msplr/PolyPot/graphics/rendering/adapter.png

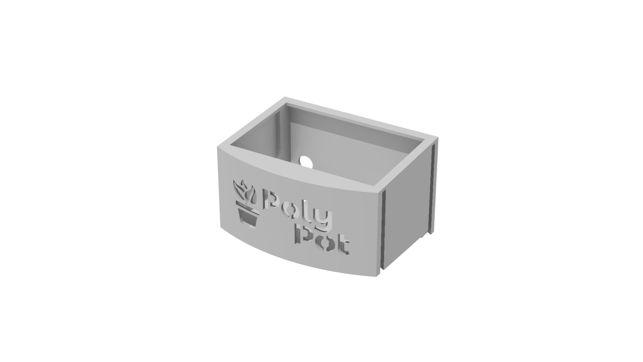
graphics/rendering/adapter.png
