msplr/PolyPot/graphics/rendering/background.png

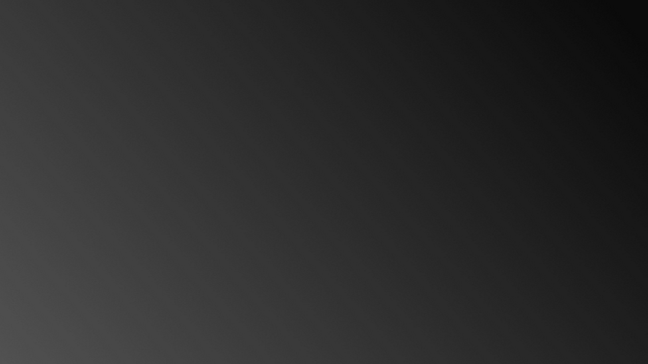
graphics/rendering/background.png
