msplr/PolyPot/graphics/rendering/module.png

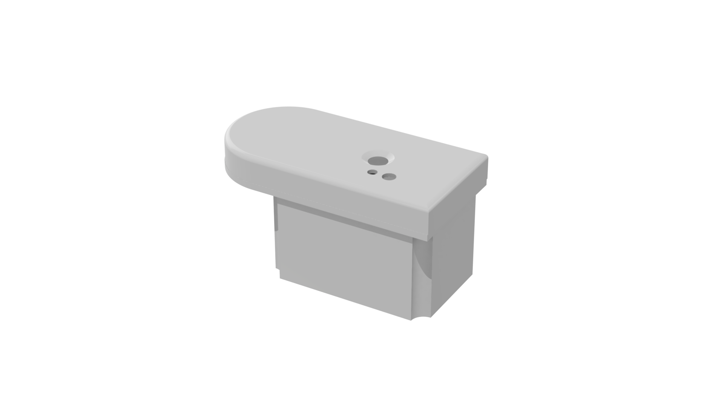
graphics/rendering/module.png
