msplr/PolyPot/graphics/rendering/plant+water_tank+adapter+module.png

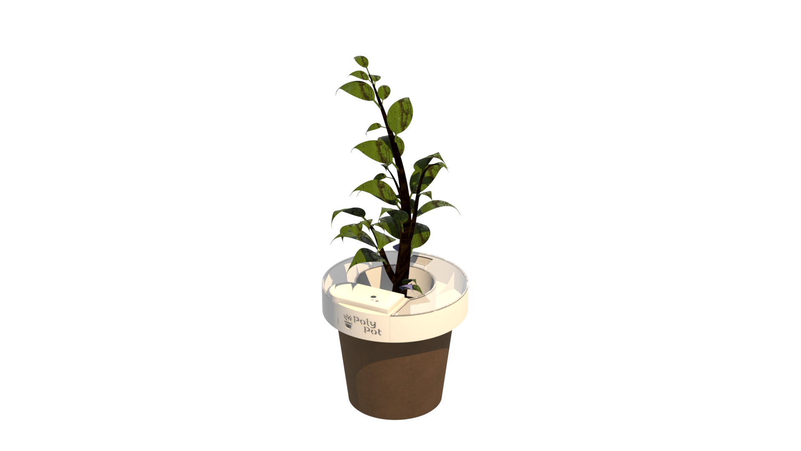
graphics/rendering/plant+water_tank+adapter+module.png
