msplr/PolyPot/graphics/rendering/polypot.png

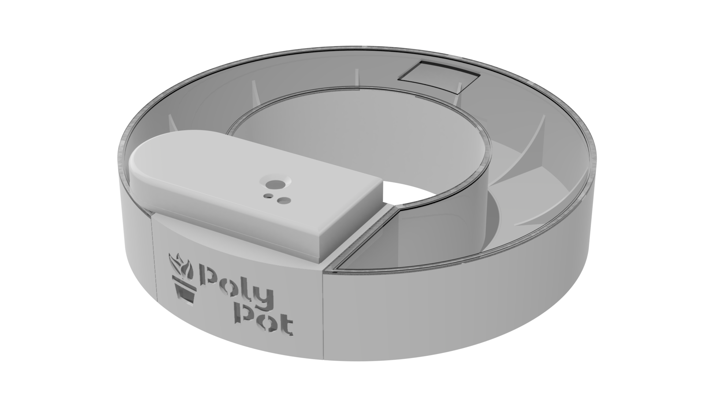
graphics/rendering/polypot.png
