msplr/PolyPot/graphics/rendering/polypot_exploded.png

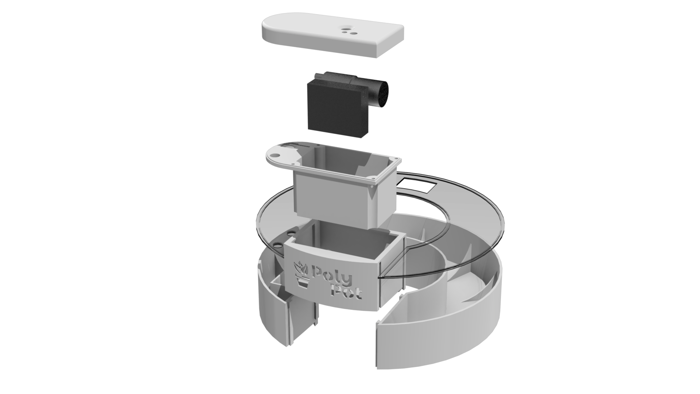
graphics/rendering/polypot_exploded.png
