msplr/PolyPot/graphics/screenshots/configuration.png

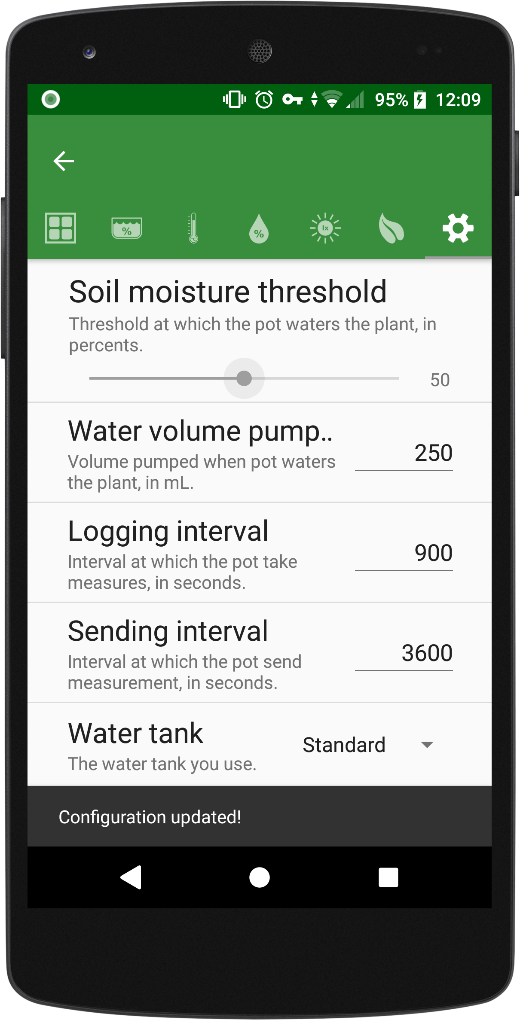
graphics/screenshots/configuration.png
