msplr/PolyPot/graphics/screenshots/features_about.png

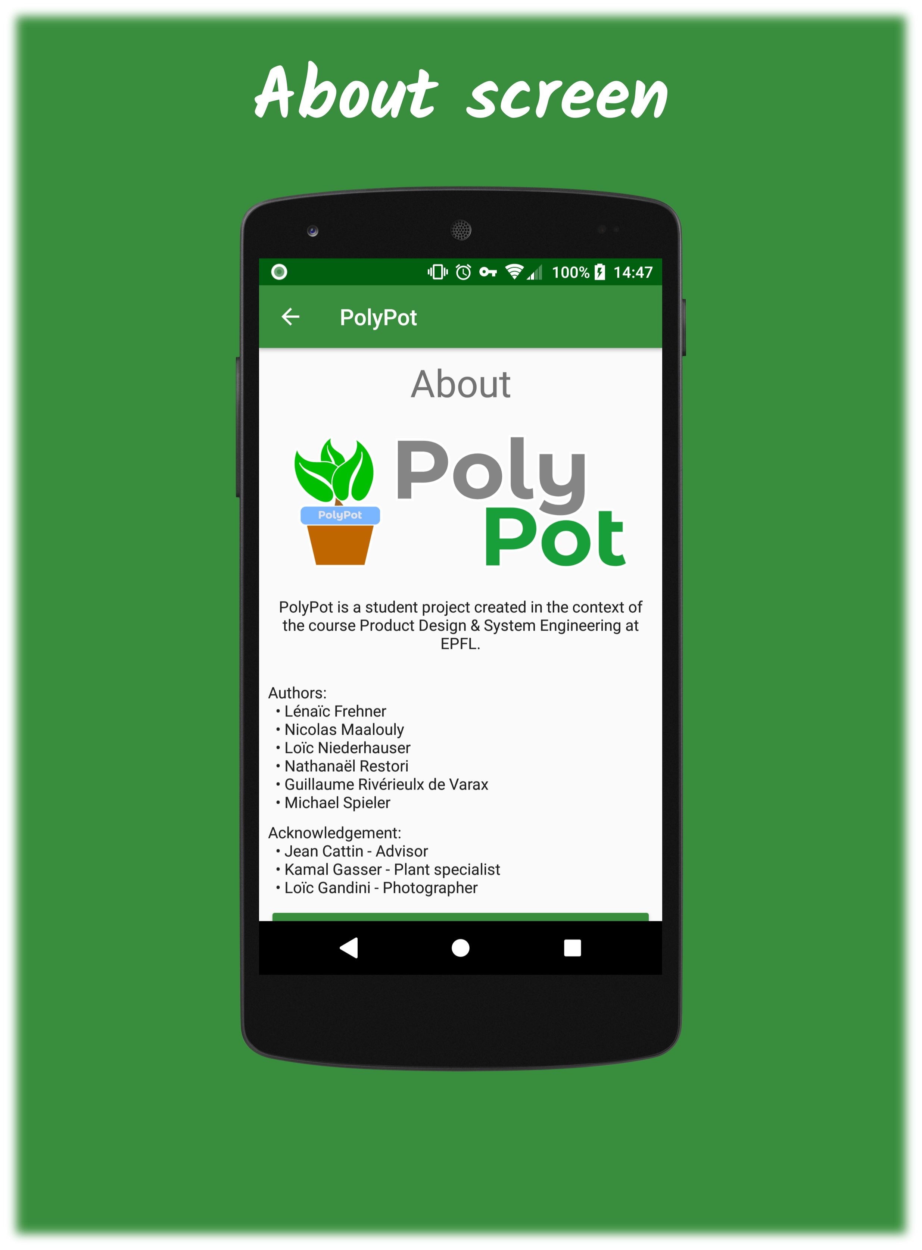
graphics/screenshots/features_about.png
