msplr/PolyPot/graphics/screenshots/features_configuration.png

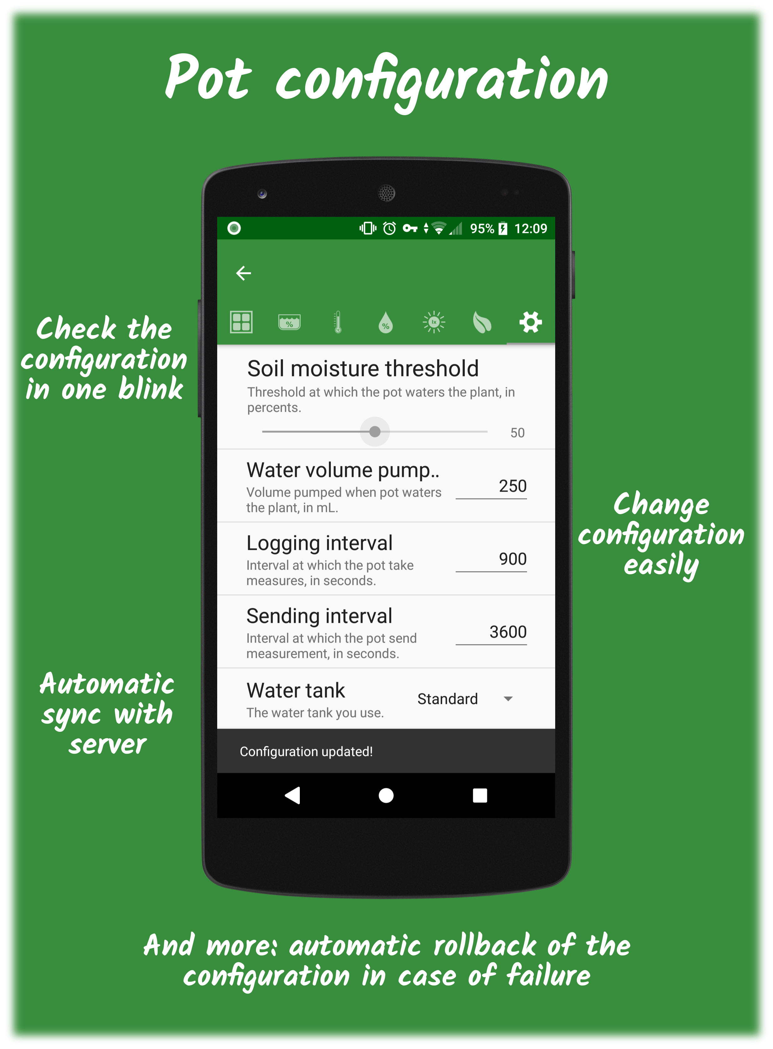
graphics/screenshots/features_configuration.png
