msplr/PolyPot/graphics/screenshots/features_homescreen.png

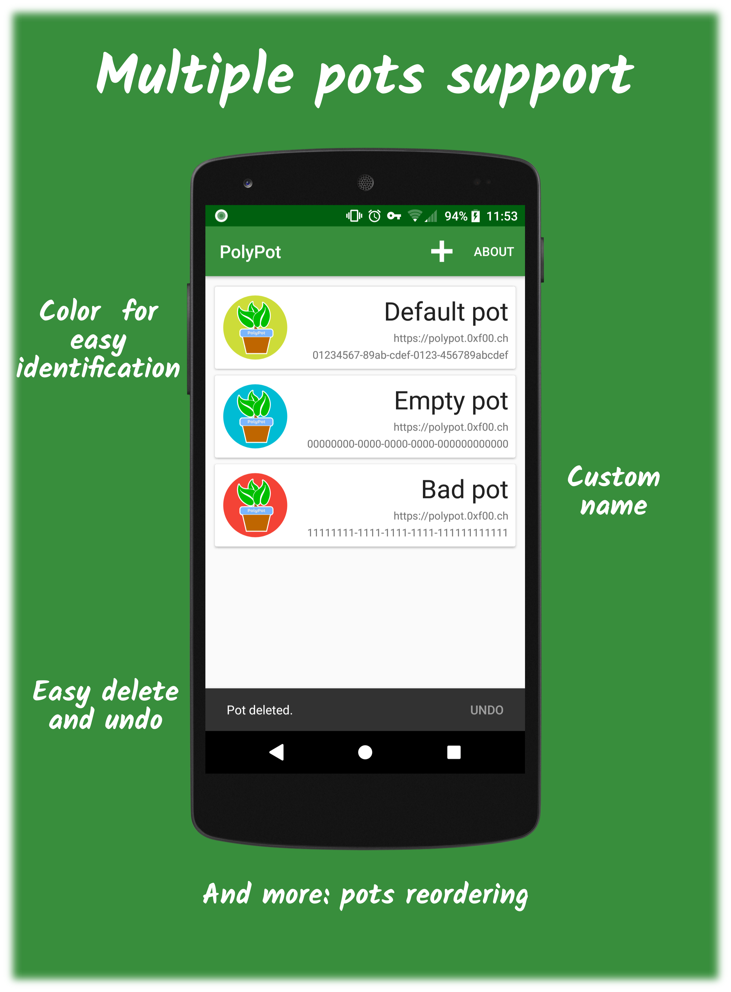
graphics/screenshots/features_homescreen.png
