msplr/PolyPot/graphics/screenshots/features_luminosity.png

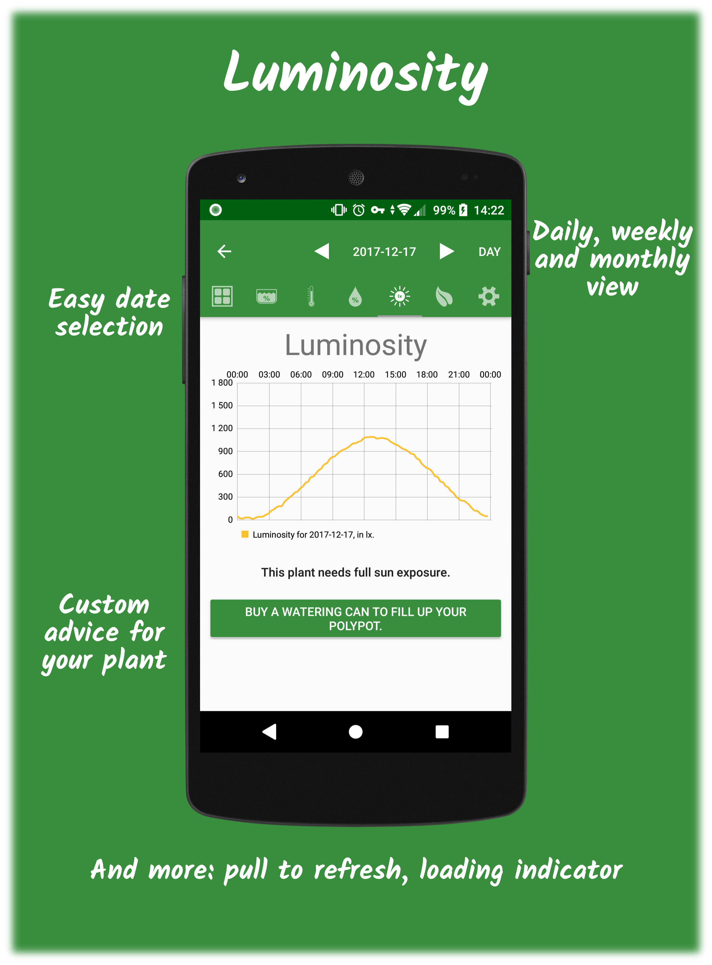
graphics/screenshots/features_luminosity.png
