msplr/PolyPot/graphics/screenshots/features_notifications.png

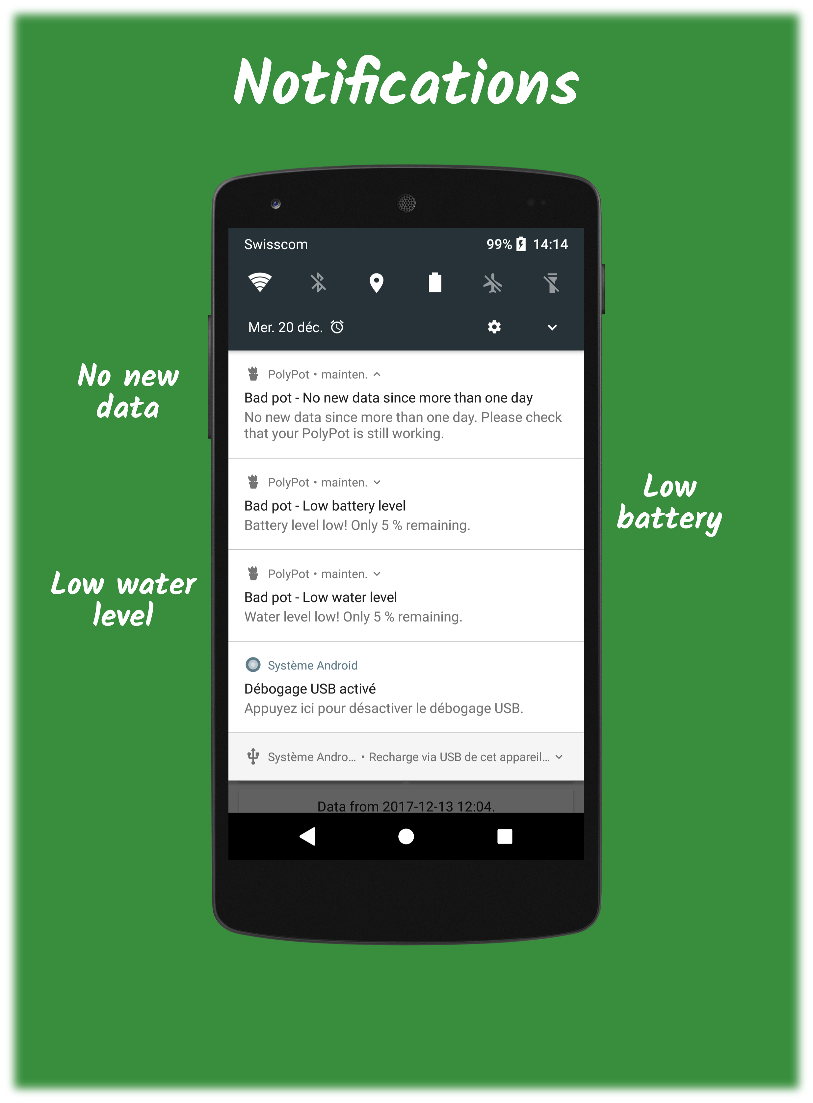
graphics/screenshots/features_notifications.png
