msplr/PolyPot/graphics/screenshots/features_plant.png

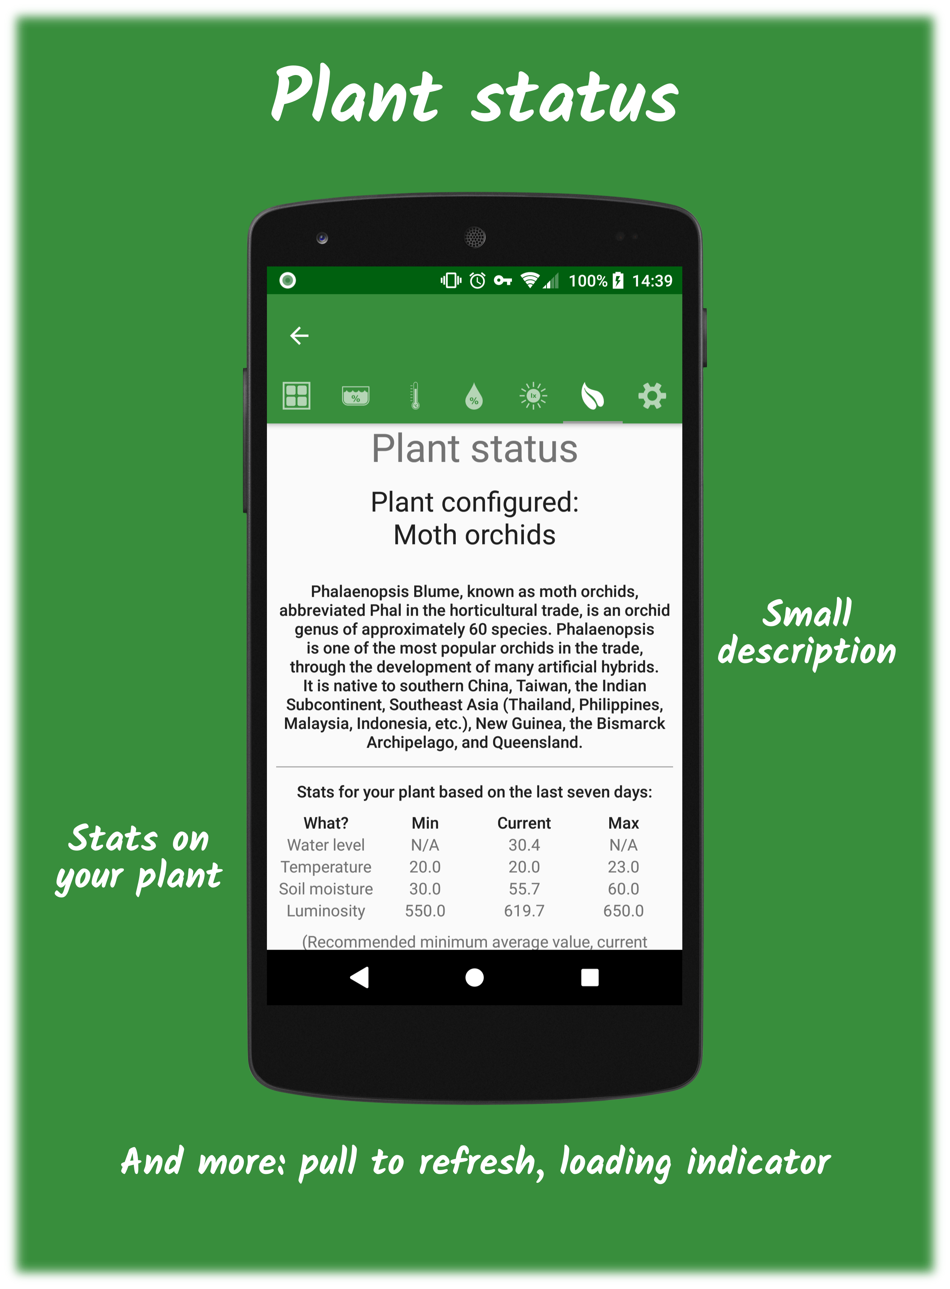
graphics/screenshots/features_plant.png
