msplr/PolyPot/graphics/screenshots/features_summary.png

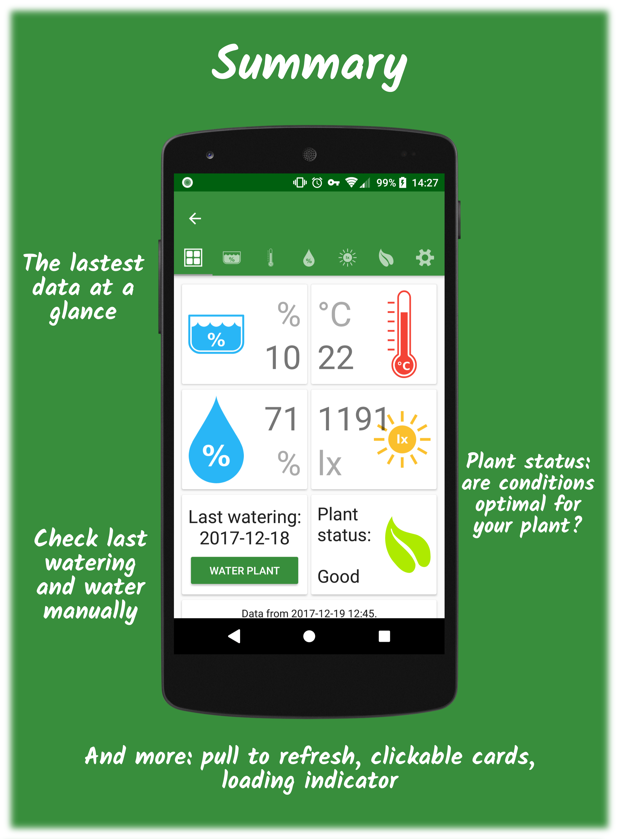
graphics/screenshots/features_summary.png
