msplr/PolyPot/graphics/screenshots/homescreen.png

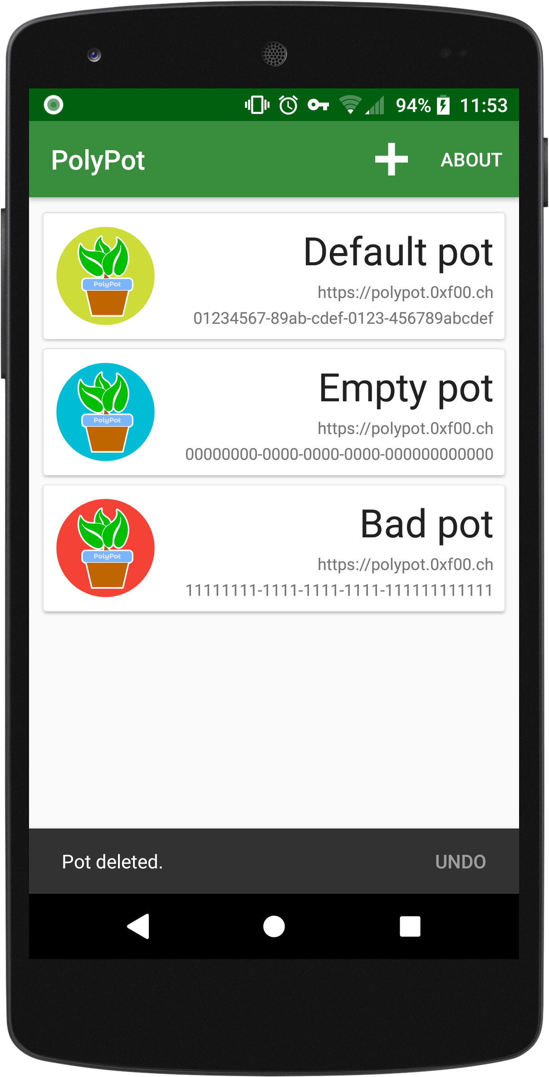
graphics/screenshots/homescreen.png
