msplr/PolyPot/graphics/screenshots/luminosity.png

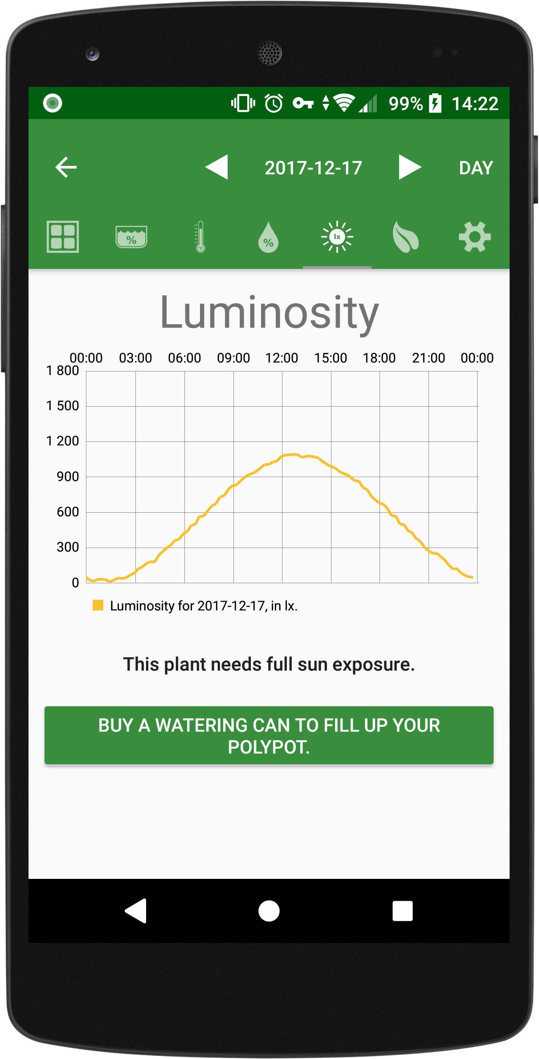
graphics/screenshots/luminosity.png
