msplr/PolyPot/graphics/screenshots/notifications.png

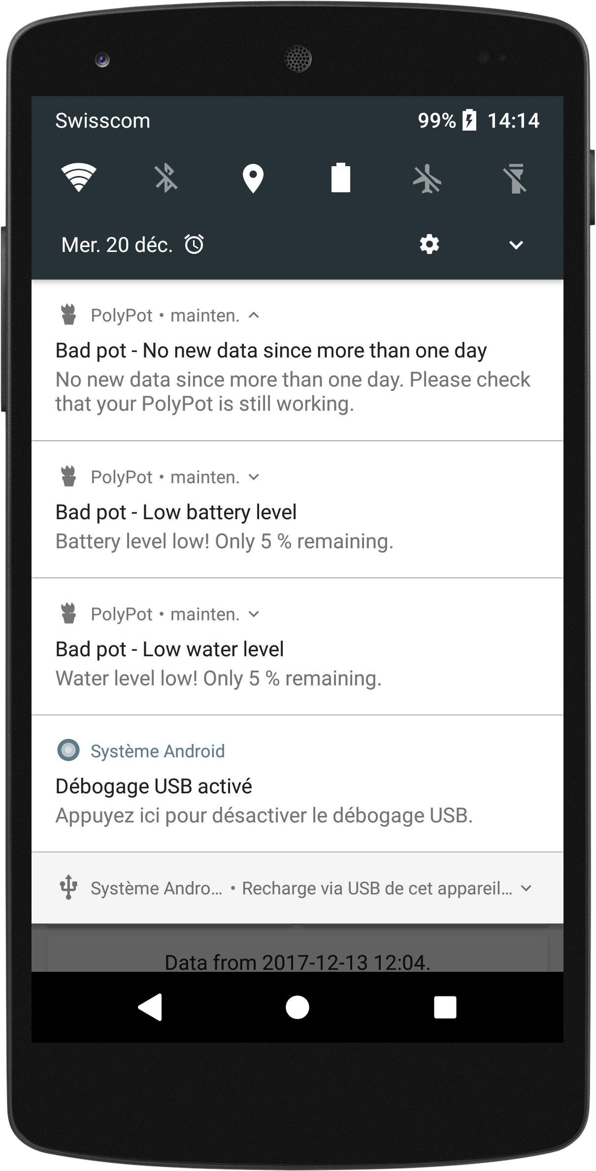
graphics/screenshots/notifications.png
