msplr/PolyPot/graphics/screenshots/plant.png

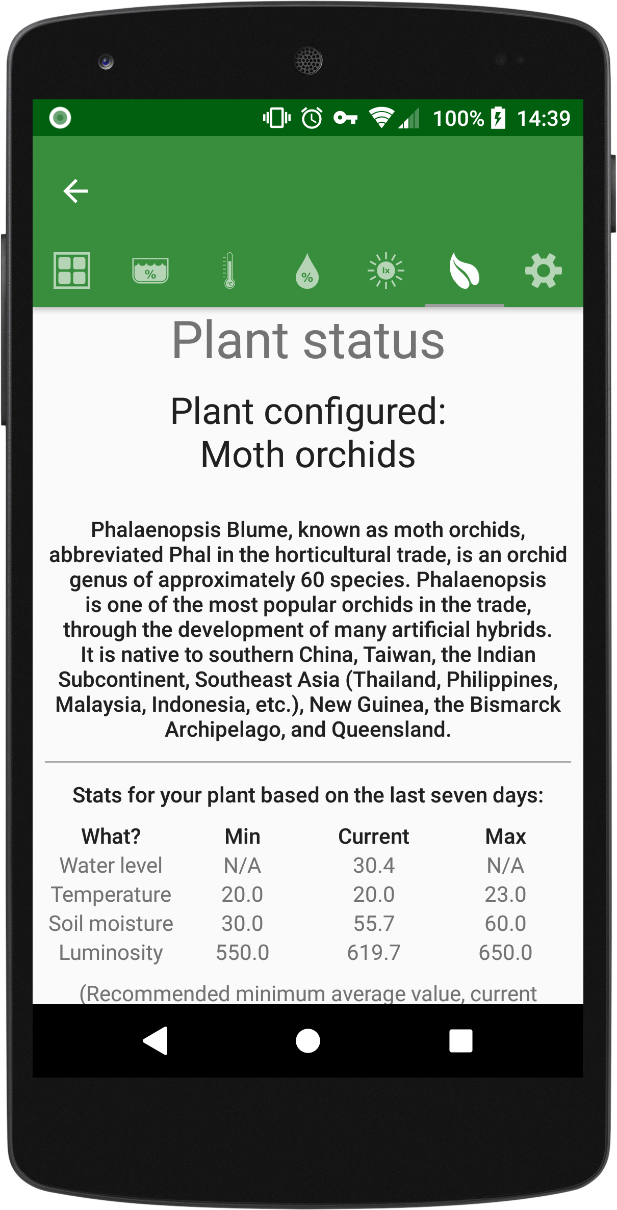
graphics/screenshots/plant.png
