msplr/PolyPot/graphics/screenshots/soil_moisture.png

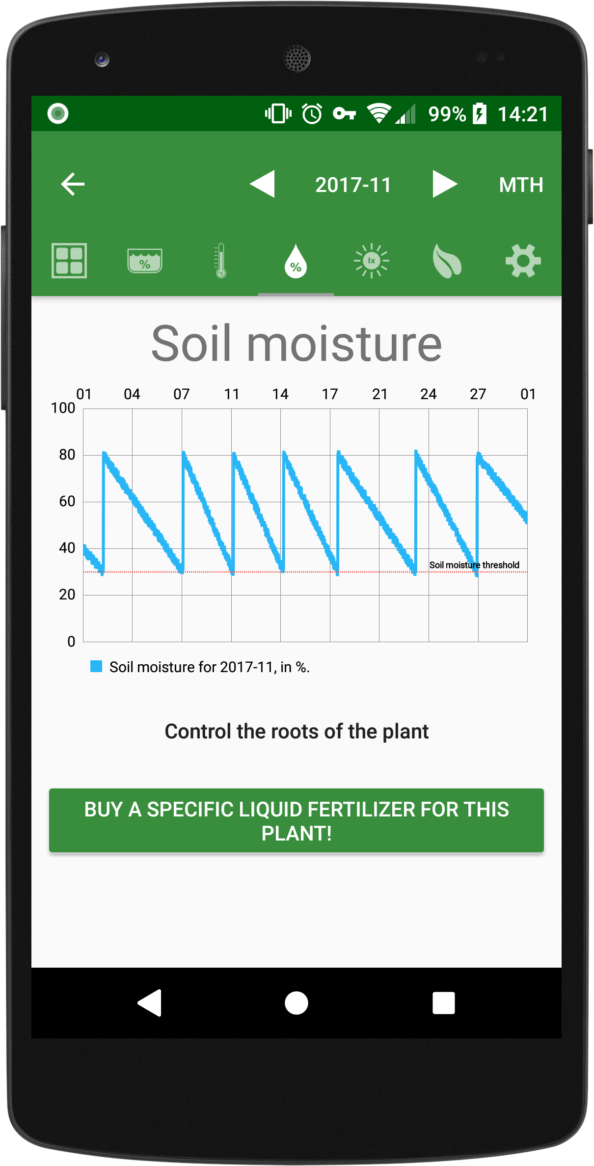
graphics/screenshots/soil_moisture.png
