msplr/PolyPot/graphics/screenshots/summary.png

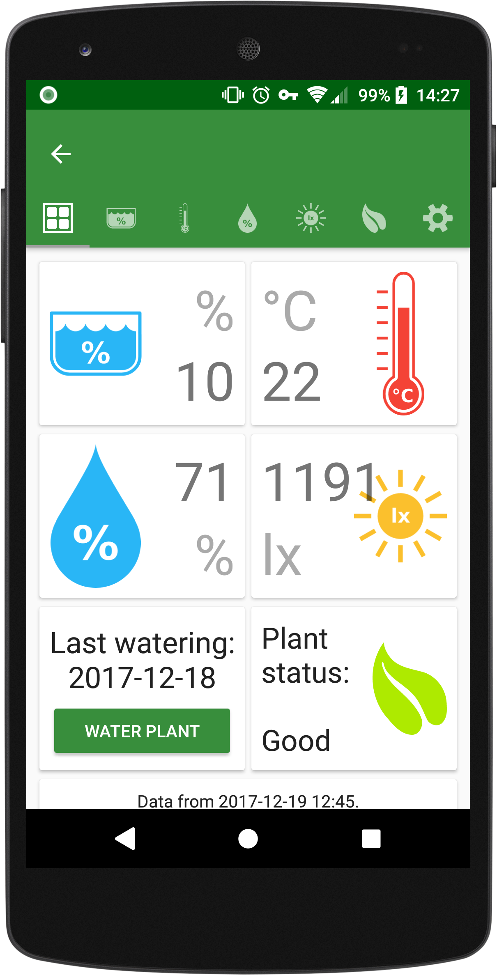
graphics/screenshots/summary.png
