msplr/PolyPot/graphics/screenshots/temperature.png

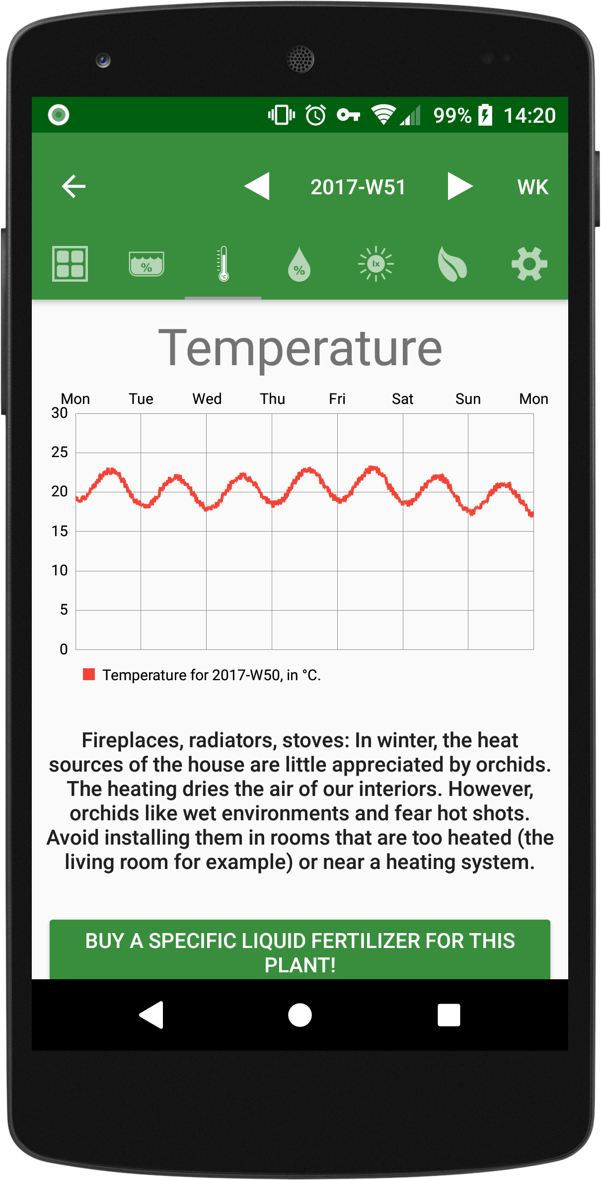
graphics/screenshots/temperature.png
