msplr/PolyPot/graphics/screenshots/water_level.png

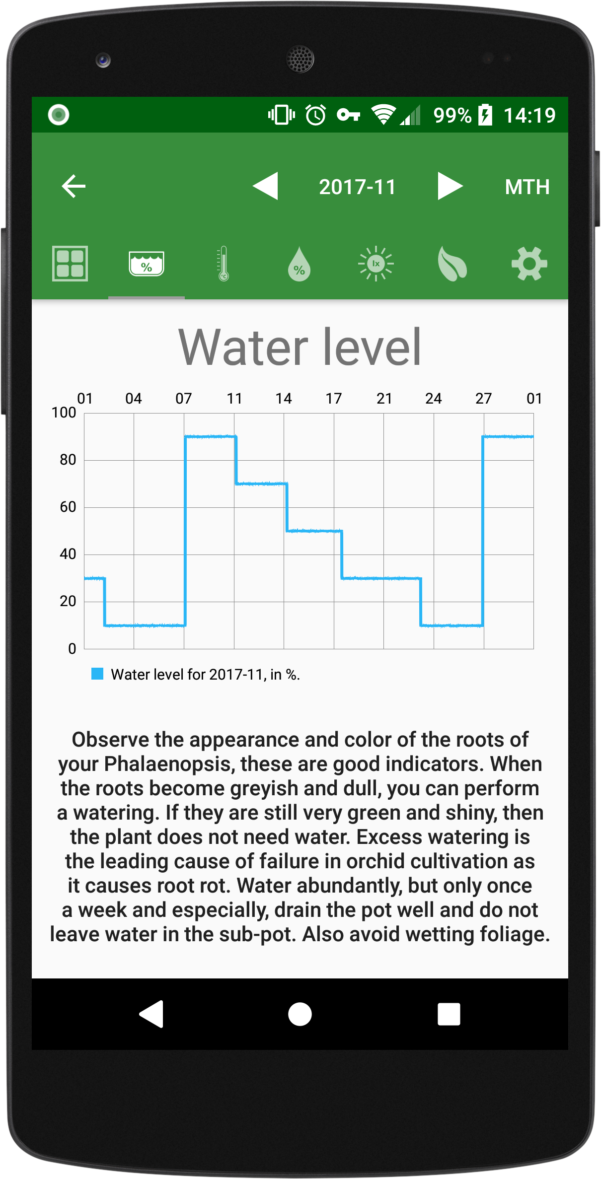
graphics/screenshots/water_level.png
