msplr/PolyPot/graphics/screenshots/features_setup_and_add.png

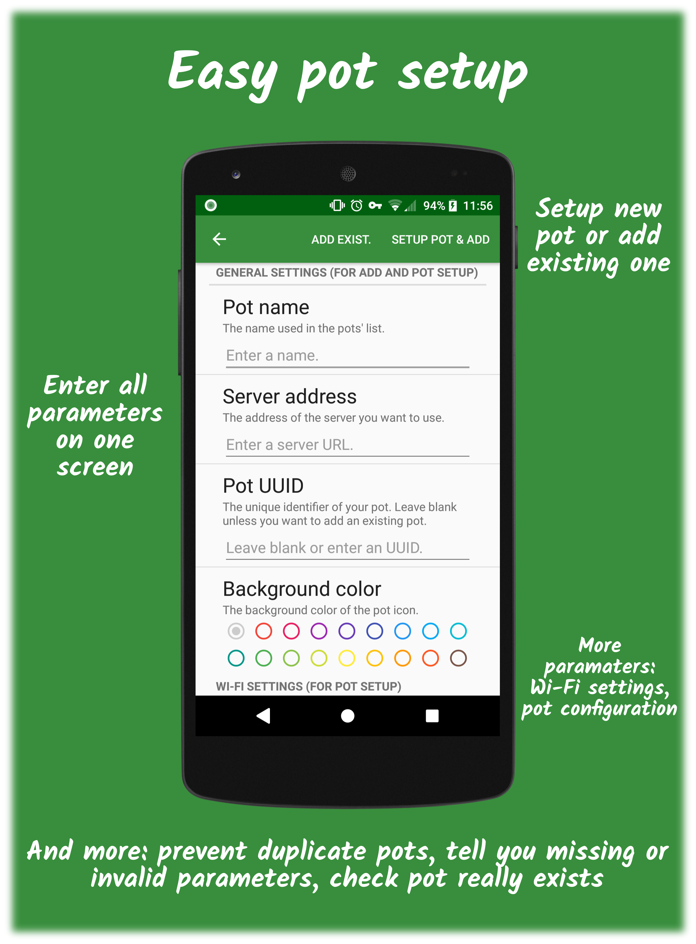
graphics/screenshots/features_setup_and_add.png
