msplr/PolyPot/graphics/screenshots/features_setup_progress.png

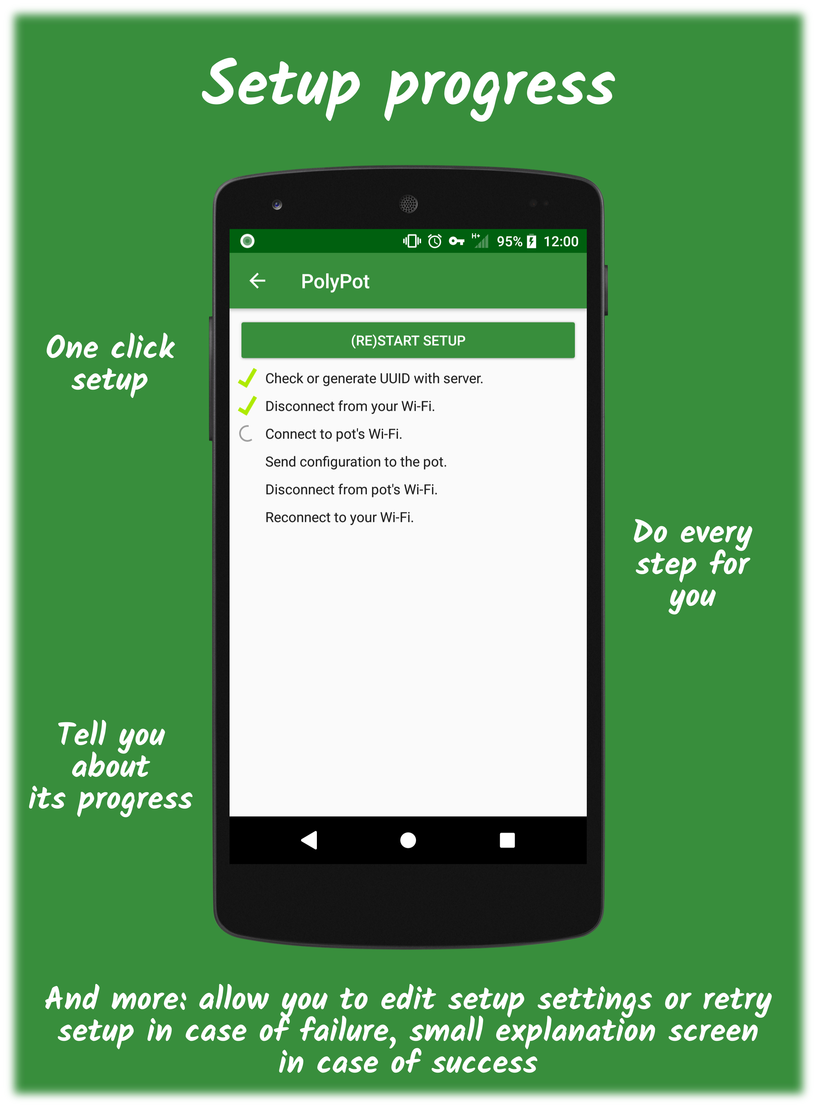
graphics/screenshots/features_setup_progress.png
