msplr/PolyPot/graphics/screenshots/setup_and_add.png

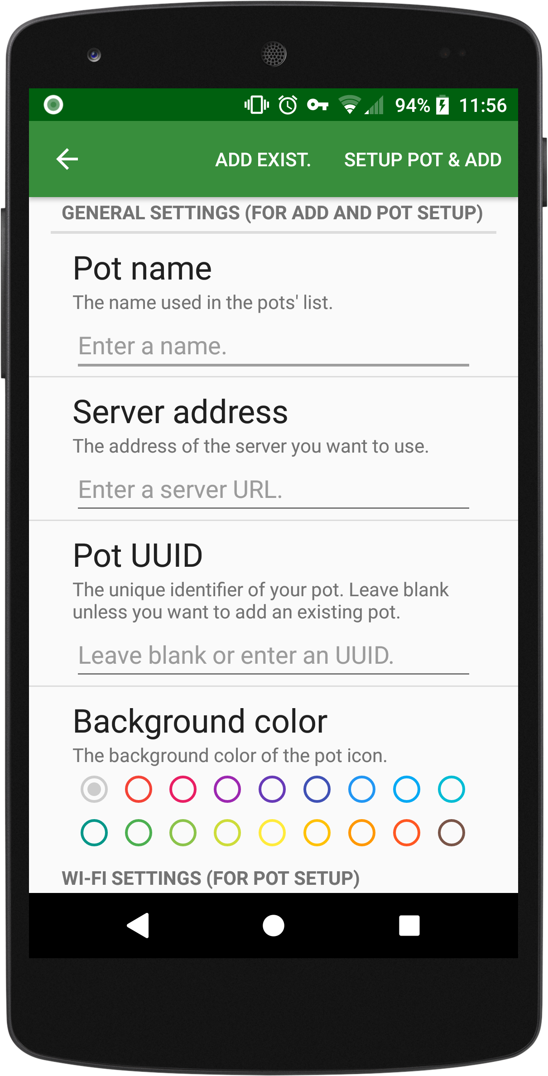
graphics/screenshots/setup_and_add.png
