msplr/PolyPot/graphics/screenshots/setup_progress.png

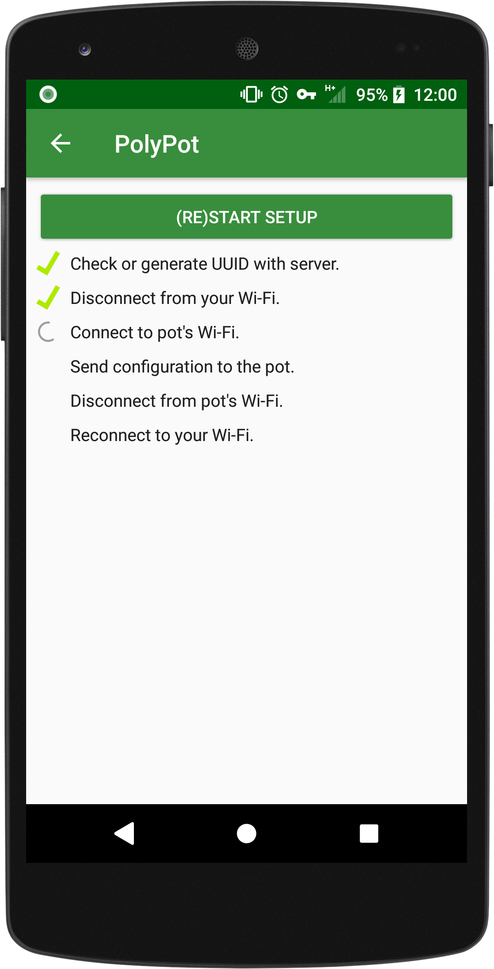
graphics/screenshots/setup_progress.png
