msplr/PolyPot/smartphone/app/src/main/java/ch/epfl/pdse/polypotapp/PreferenceSpinner.java

package ch.epfl.pdse.polypotapp;

import android.content.Context;
import android.content.res.TypedArray;
import android.support.v7.preference.Preference;
import android.support.v7.preference.PreferenceViewHolder;
import android.util.AttributeSet;
import android.view.View;
import android.widget.AdapterView;
import android.widget.ArrayAdapter;
import android.widget.Spinner;

public class PreferenceSpinner extends Preference implements Preference.OnPreferenceChangeListener,AdapterView.OnItemSelectedListener  {
    private Spinner mSpinner;
    private ArrayAdapter<CharSequence> mArrayAdapter;

    private final int mArray;

    private String mValue;

    public PreferenceSpinner(Context context) {
        // Delegate to other constructor
        this(context, null);
    }

    public PreferenceSpinner(Context context, AttributeSet attrs) {
        this(context, attrs, 0);
    }

    public PreferenceSpinner(Context context, AttributeSet attrs, int defStyleAttr) {
        super(context, attrs, defStyleAttr);
        //setLayoutResource(R.layout.layout_preference);
        setWidgetLayoutResource(R.layout.preference_spinner);

        TypedArray a = context.obtainStyledAttributes(attrs, R.styleable.PreferenceSpinner);
        mArray = a.getResourceId(R.styleable.PreferenceSpinner_array, R.array.empty);
        a.recycle();
    }

    @Override
    public void onBindViewHolder(PreferenceViewHolder holder) {
        super.onBindViewHolder(holder);

        holder.itemView.setClickable(false);

        mSpinner = (Spinner) holder.findViewById(R.id.spinner);

        ArrayAdapter<CharSequence> adapter = ArrayAdapter.createFromResource(getContext(), mArray, android.R.layout.simple_spinner_item);
        adapter.setDropDownViewResource(android.R.layout.simple_spinner_dropdown_item);
        mSpinner.setAdapter(adapter);

        mSpinner.setSelection(adapter.getPosition(mValue));

        mSpinner.setOnItemSelectedListener(this);
    }

    @Override
    public void onItemSelected(AdapterView<?> adapterView, View view, int pos, long id) {
        //TODO: more fluid experience
        View focus = view.findFocus();
        mSpinner.setFocusable(true);
        mSpinner.setFocusableInTouchMode(true);
        if(focus != null) {
            focus.requestFocus();
        }

        mValue = (String) adapterView.getItemAtPosition(pos);
        persistString(mValue);
    }

    @Override
    public void onNothingSelected(AdapterView<?> adapterView) {
    }

    @Override
    protected Object onGetDefaultValue(TypedArray a, int index) {
        return a.getString(index);
    }

    @Override
    protected void onSetInitialValue(boolean restorePersistedValue, Object defaultValue) {
        if (restorePersistedValue) {
            // Restore existing state
            mValue = this.getPersistedString("");
        } else {
            // Set default state from the XML attribute
            mValue = (String) defaultValue;
            persistString(mValue);
        }
    }

    @Override
    public boolean onPreferenceChange(Preference preference, Object newValue) {
        mValue = (String) newValue;

        mSpinner.setSelection(mArrayAdapter.getPosition(mValue));

        return true;
    }
}
